frosty6742/frozen-slimes-v2/Pictures/221204855-9bce6008-605c-4c25-83e0-810afc768479.png

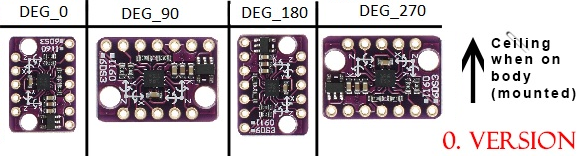
Pictures/221204855-9bce6008-605c-4c25-83e0-810afc768479.png
