frosty6742/frozen-slimes-v2/Pictures/227601854-59f1a4b9-e775-4e03-859e-9156e86dac59.png

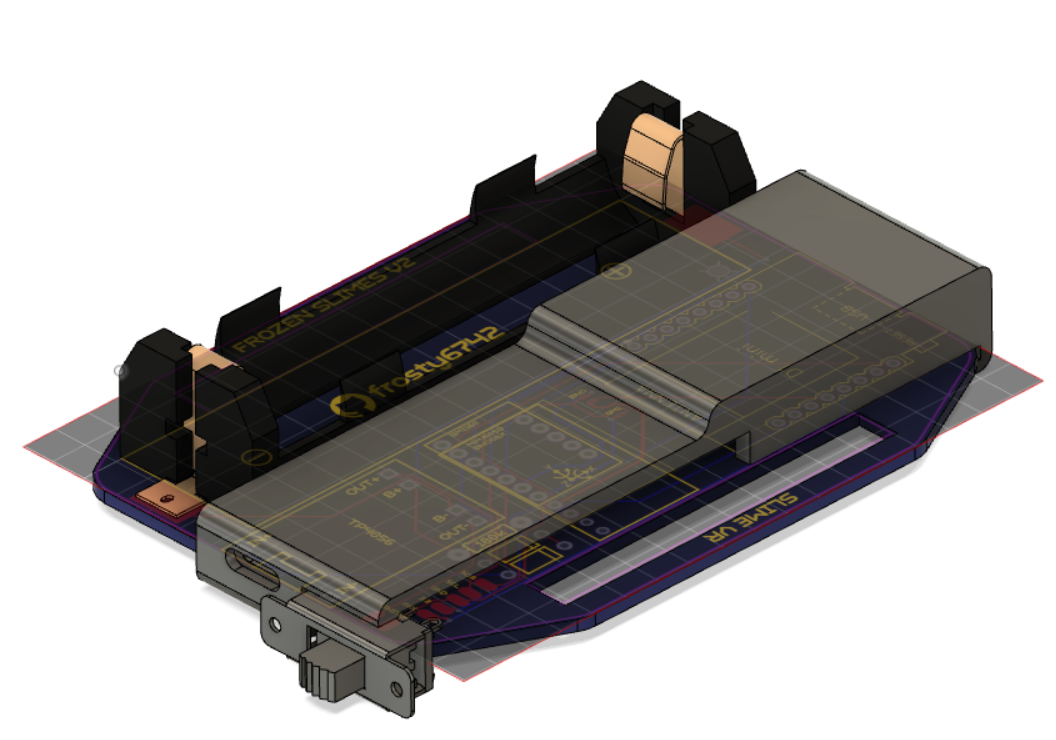
Pictures/227601854-59f1a4b9-e775-4e03-859e-9156e86dac59.png
