frosty6742/frozen-slimes-v2/Pictures/227603217-12ec5b41-bc10-43a8-856b-a48b9d3375ae.png

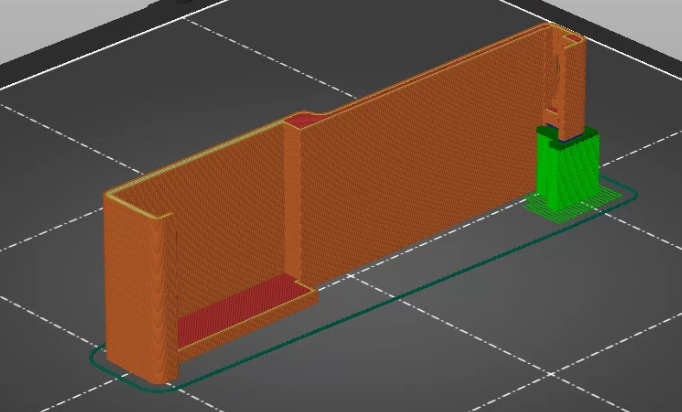
Pictures/227603217-12ec5b41-bc10-43a8-856b-a48b9d3375ae.png
