frosty6742/frozen-slimes-v2/Pictures/IMG_1062.jpg

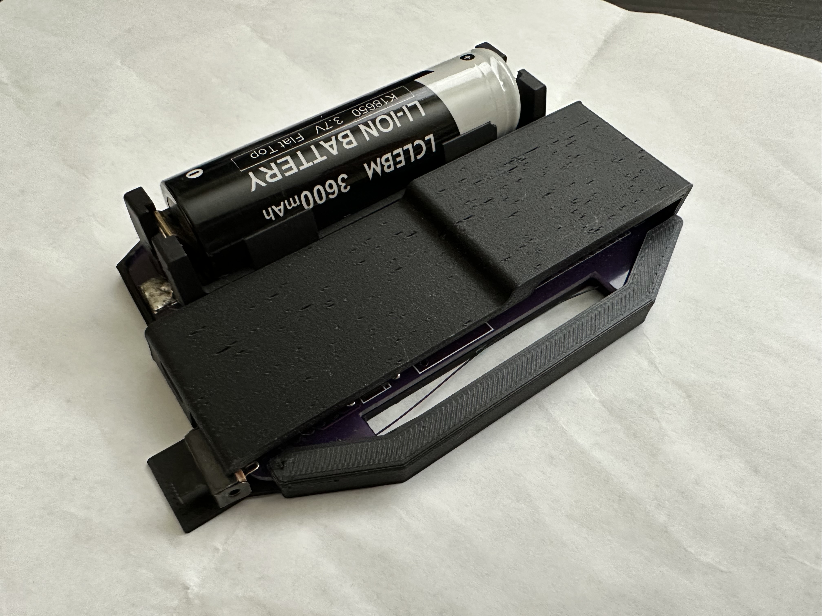
Pictures/IMG_1062.jpg
