frosty6742/frozen-slimes-v2/Pictures/IMG_1065.jpg

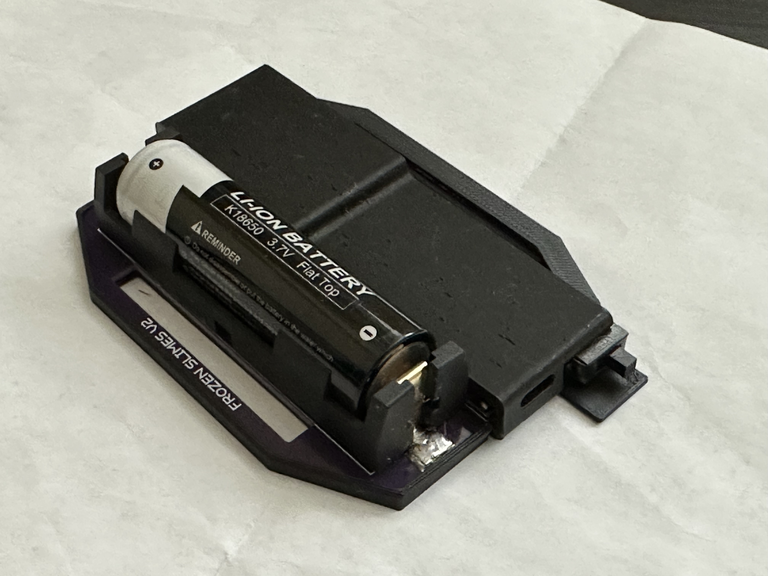
Pictures/IMG_1065.jpg
