frosty6742/frozen-slimes-v2/Pictures/pcbPicture2.png

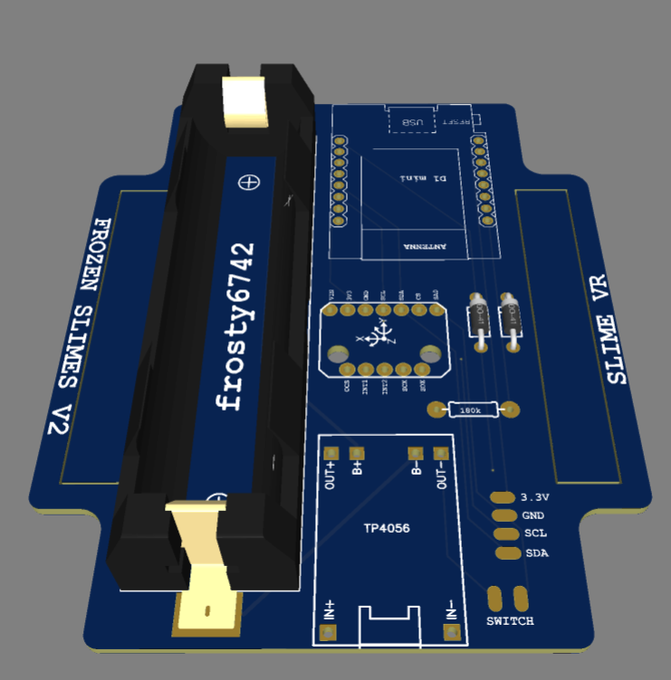
Pictures/pcbPicture2.png
