frosty6742/frozen-slimes-v2/Pictures/pcbPicture.png

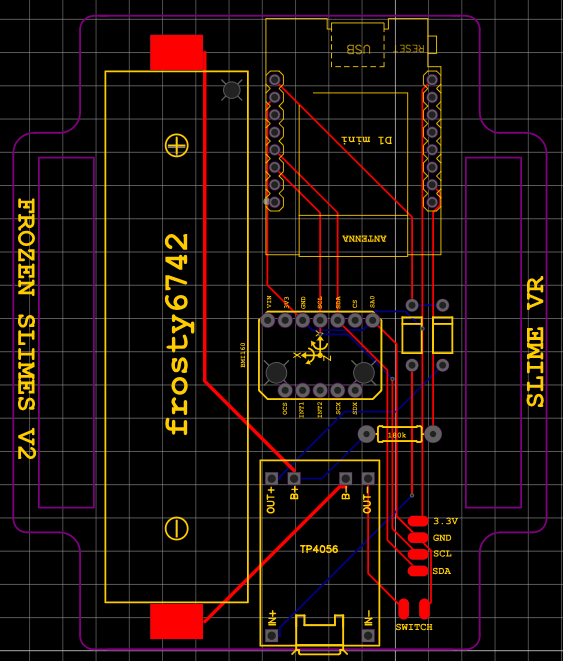
Pictures/pcbPicture.png
