frosty6742/frozen-slimes-v2/Pictures/pcbSilkScreen.png

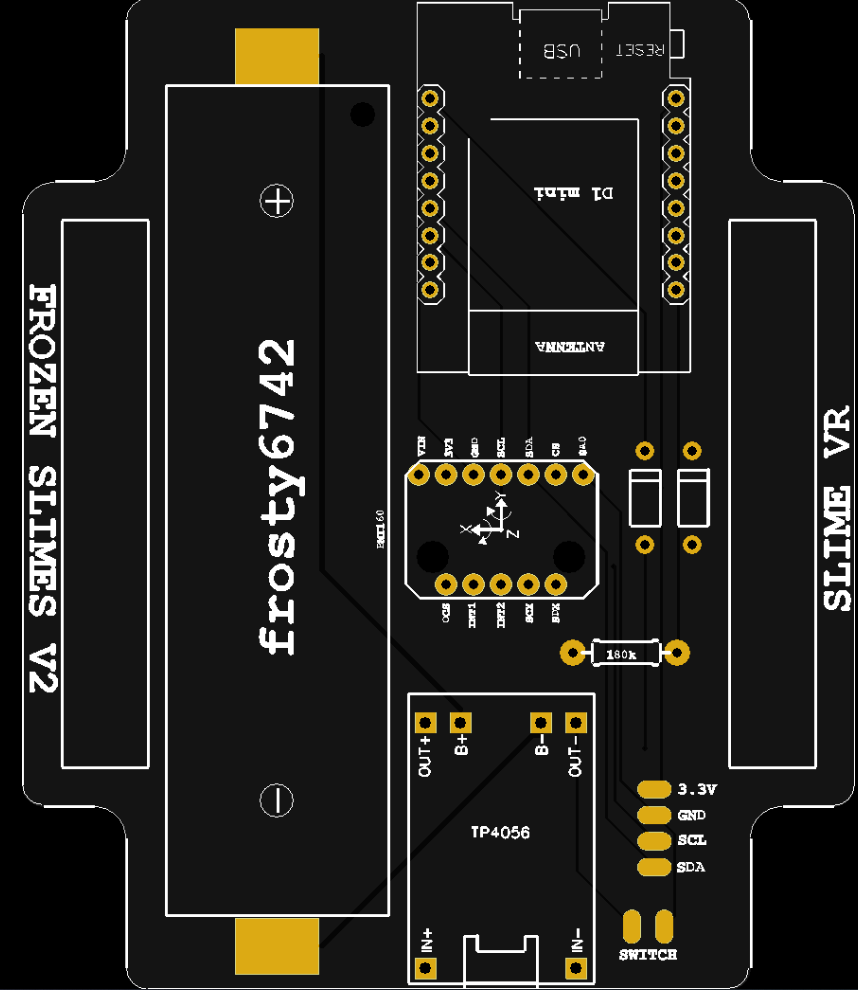
Pictures/pcbSilkScreen.png
