frosty6742/frozen-slimes-v2/Pictures/Screenshot 2023-02-10 085738.png

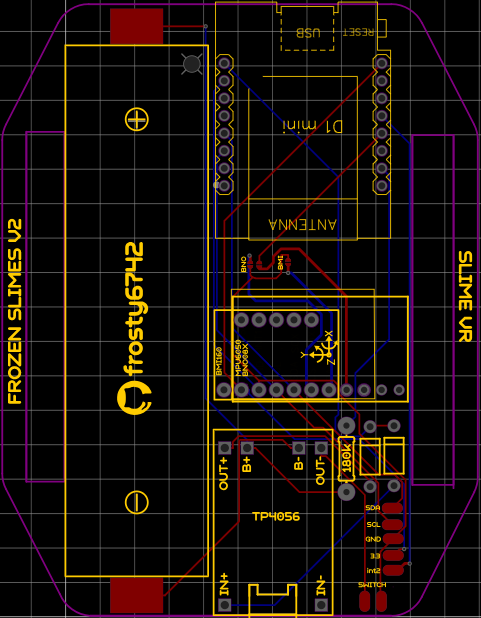
Pictures/Screenshot 2023-02-10 085738.png
