frosty6742/frozen-slimes-v2/Pictures/Screenshot 2023-06-21 091655.png

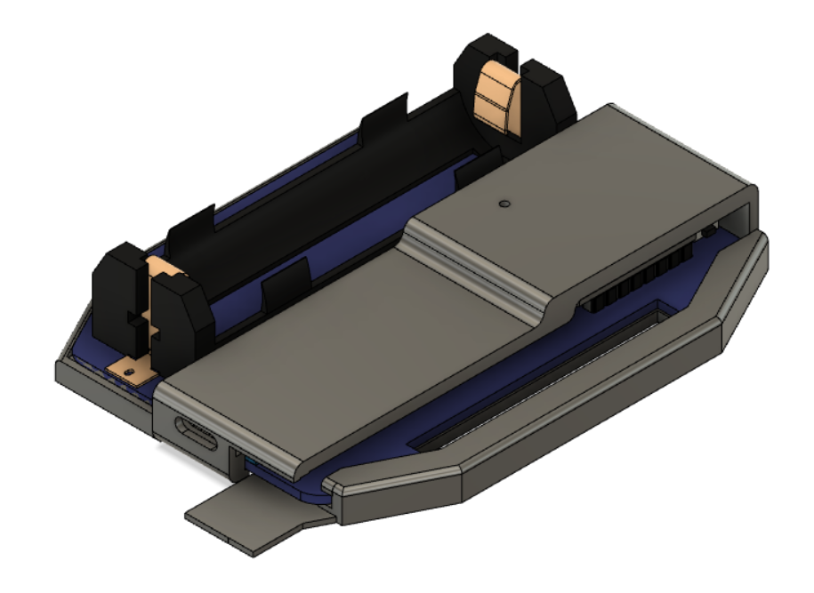
Pictures/Screenshot 2023-06-21 091655.png
