frosty6742/frozen-slimes-v2/Pictures/Screenshot 2024-02-11 134546830.png

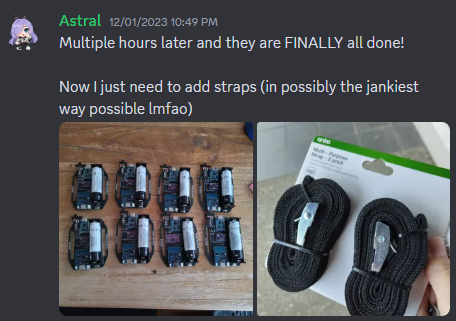
Pictures/Screenshot 2024-02-11 134546830.png
