frosty6742/frozen-slimes-v2/Pictures/Screenshot 2024-02-11 13424676546553.png

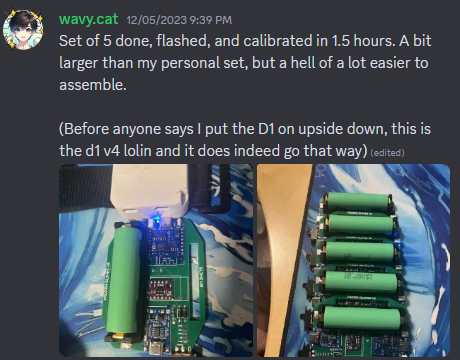
Pictures/Screenshot 2024-02-11 13424676546553.png
